TylerJulian/STM32F103RCT6-Dev-Board/DSC_0808.JPG

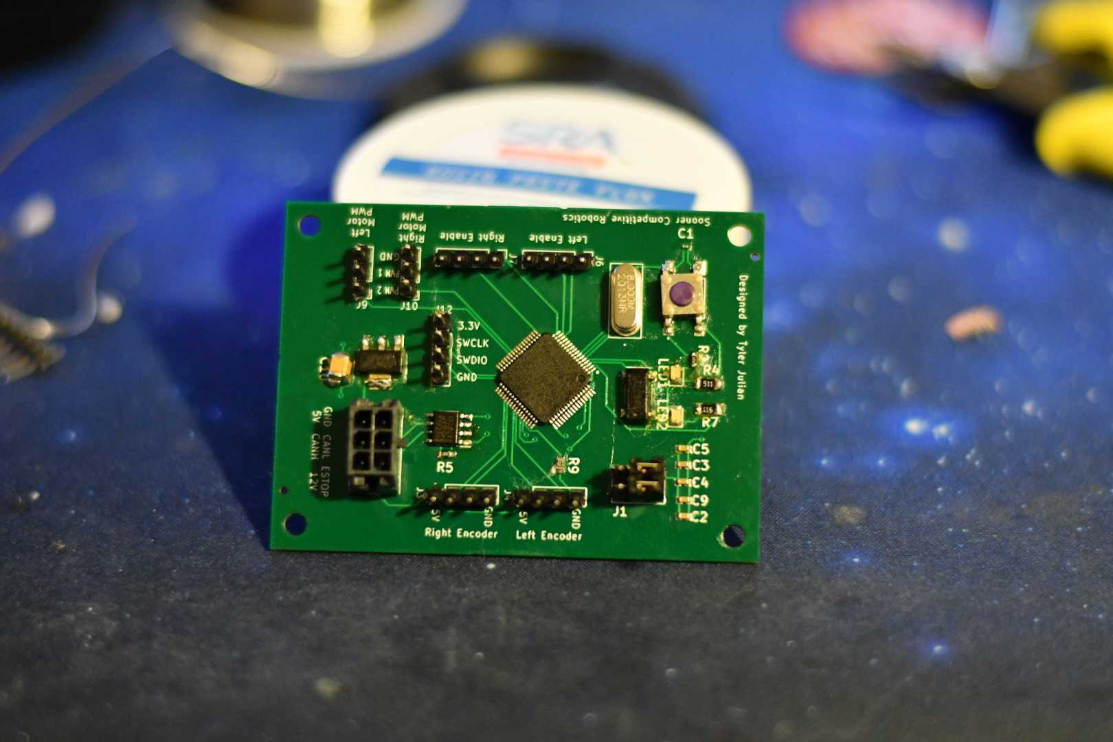
DSC_0808.JPG
